jeanbaptiste/textilo/pictures/paper.Textilo/paper-version-of-textilo2.jpg

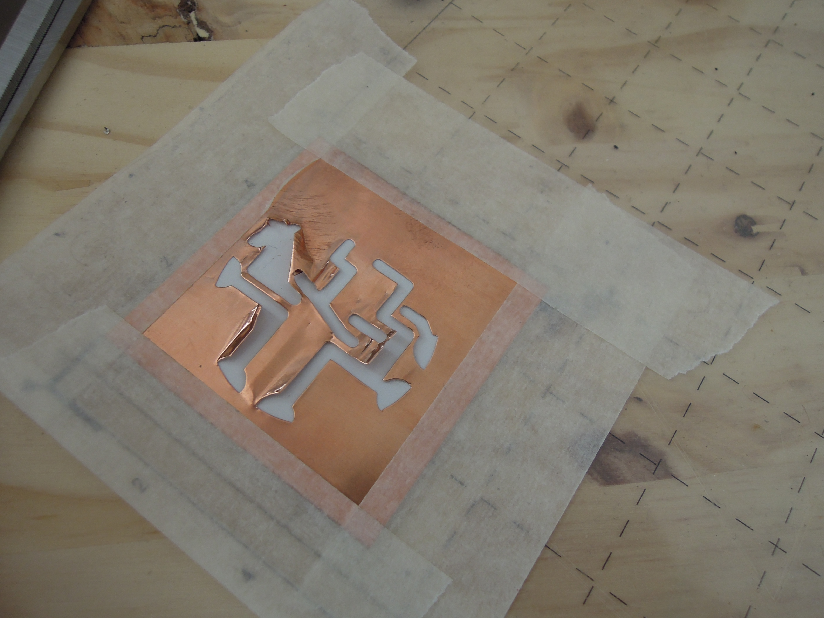
pictures/paper.Textilo/paper-version-of-textilo2.jpg
