jeanbaptiste/textilo/pictures/trial.with.Plotter/555circuit-july.jpg

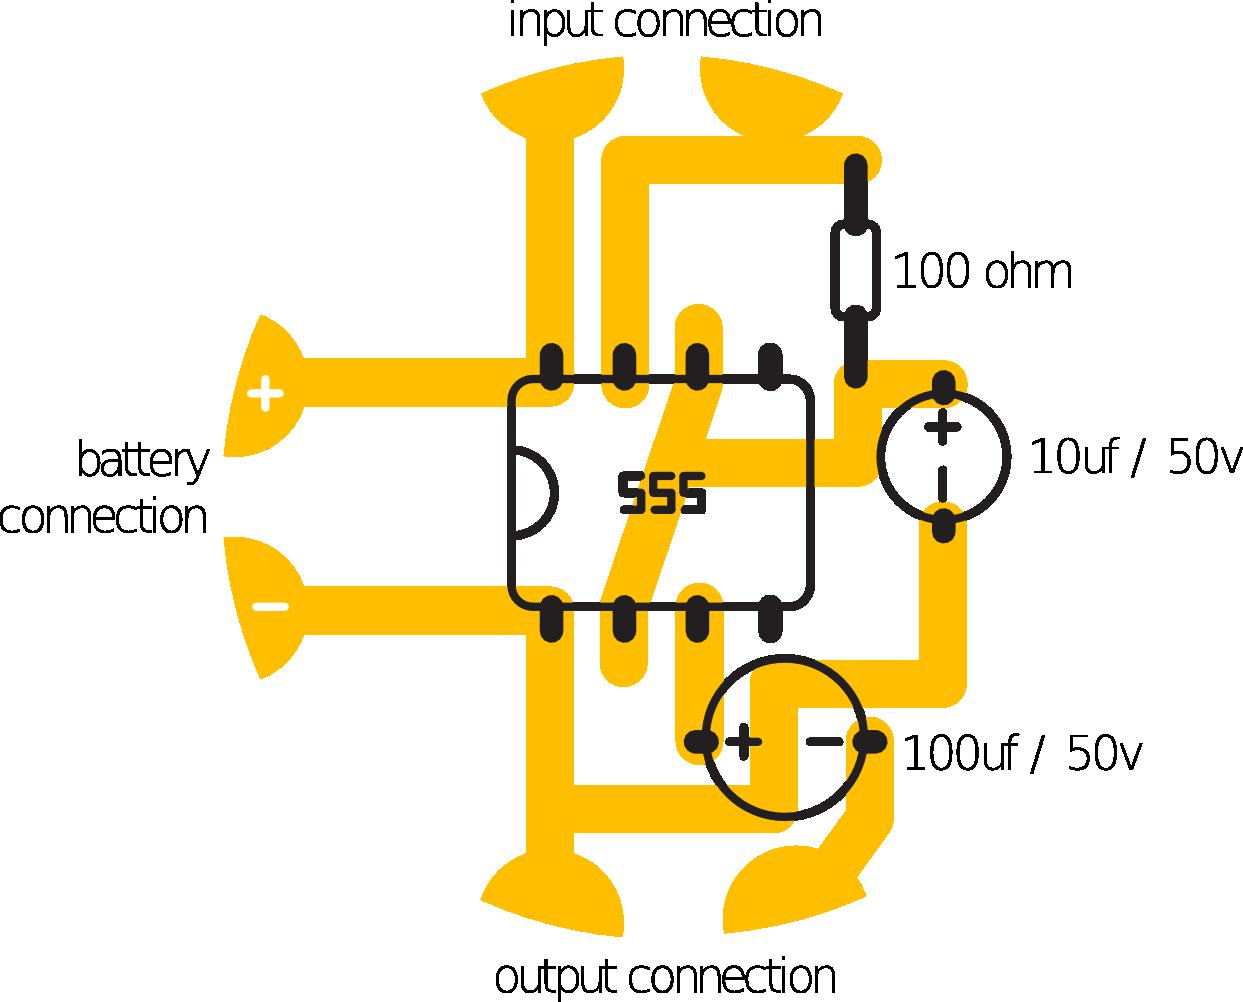
pictures/trial.with.Plotter/555circuit-july.jpg
