jeanbaptiste/textilo/pictures/trial.with.Plotter/EssaiTextilo1.jpg

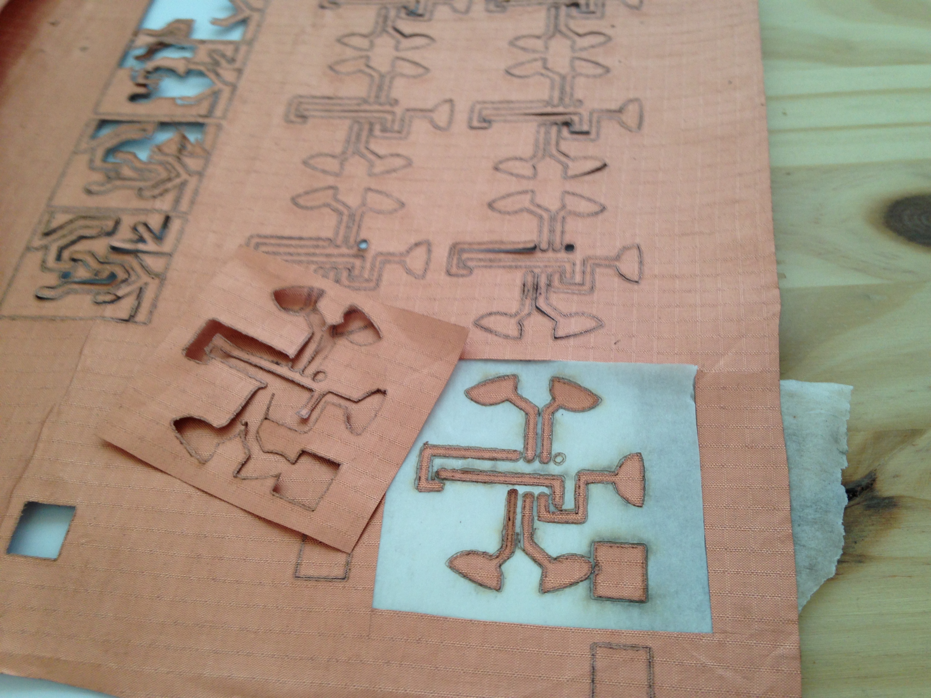
pictures/trial.with.Plotter/EssaiTextilo1.jpg
