jeanbaptiste/textilo/pictures/trial.with.Plotter/EssaiTextilo2.jpg

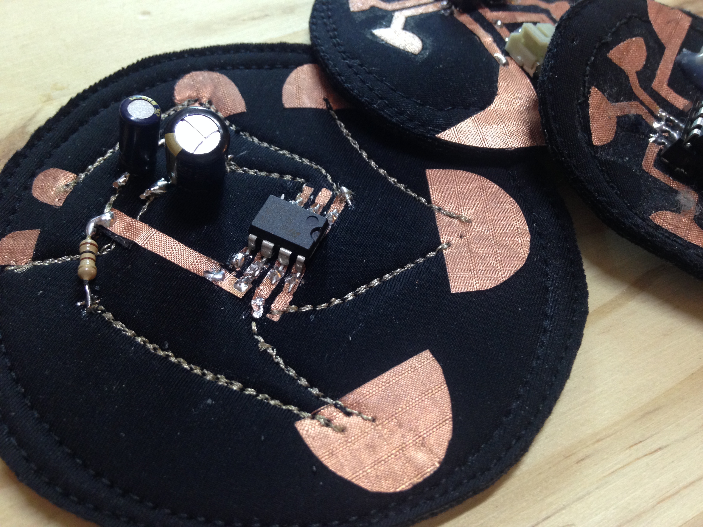
pictures/trial.with.Plotter/EssaiTextilo2.jpg
