jeanbaptiste/textilo/pictures/trial.with.Plotter/EssaiTextilo3.jpg

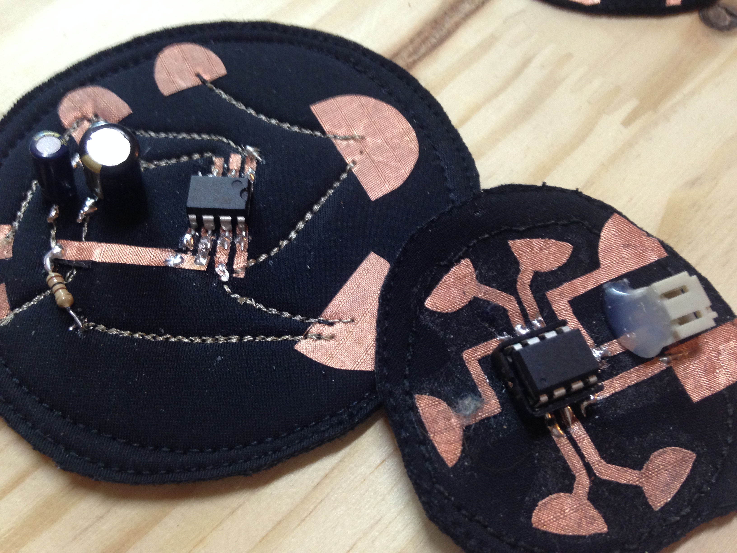
pictures/trial.with.Plotter/EssaiTextilo3.jpg
