jeanbaptiste/textilo/pictures/trial.with.Plotter/EssaiTextilo4.jpg

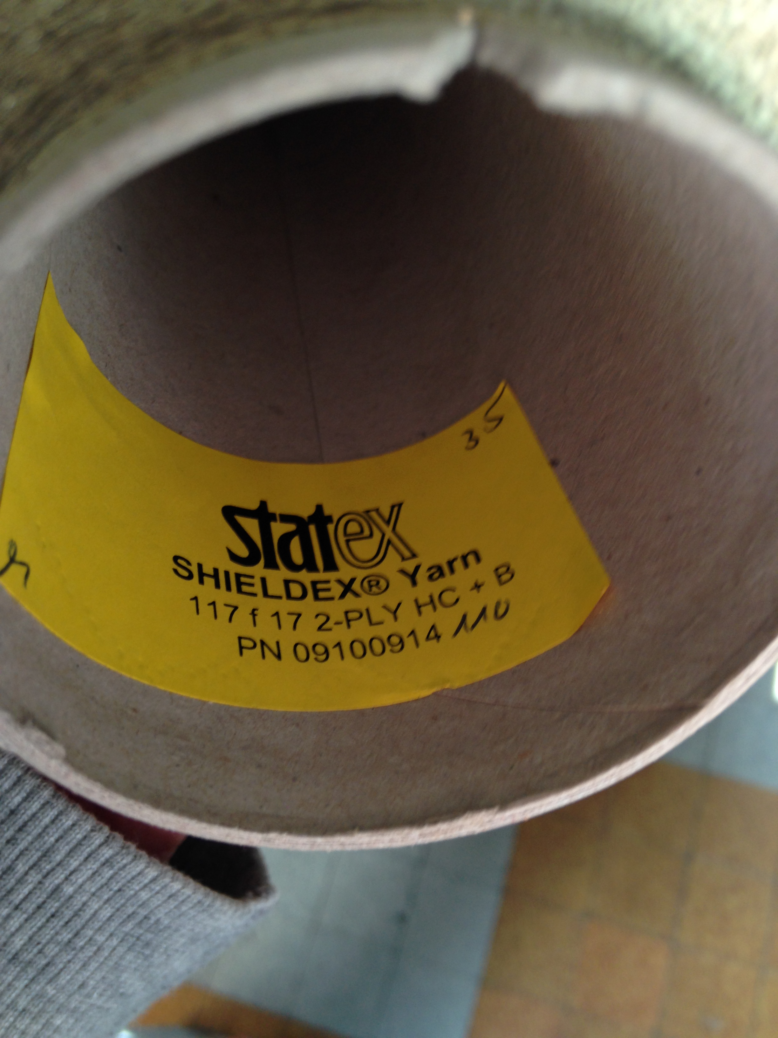
pictures/trial.with.Plotter/EssaiTextilo4.jpg
