jeanbaptiste/textilo/pictures/trial.with.Plotter/EssaiTextilo5.jpg

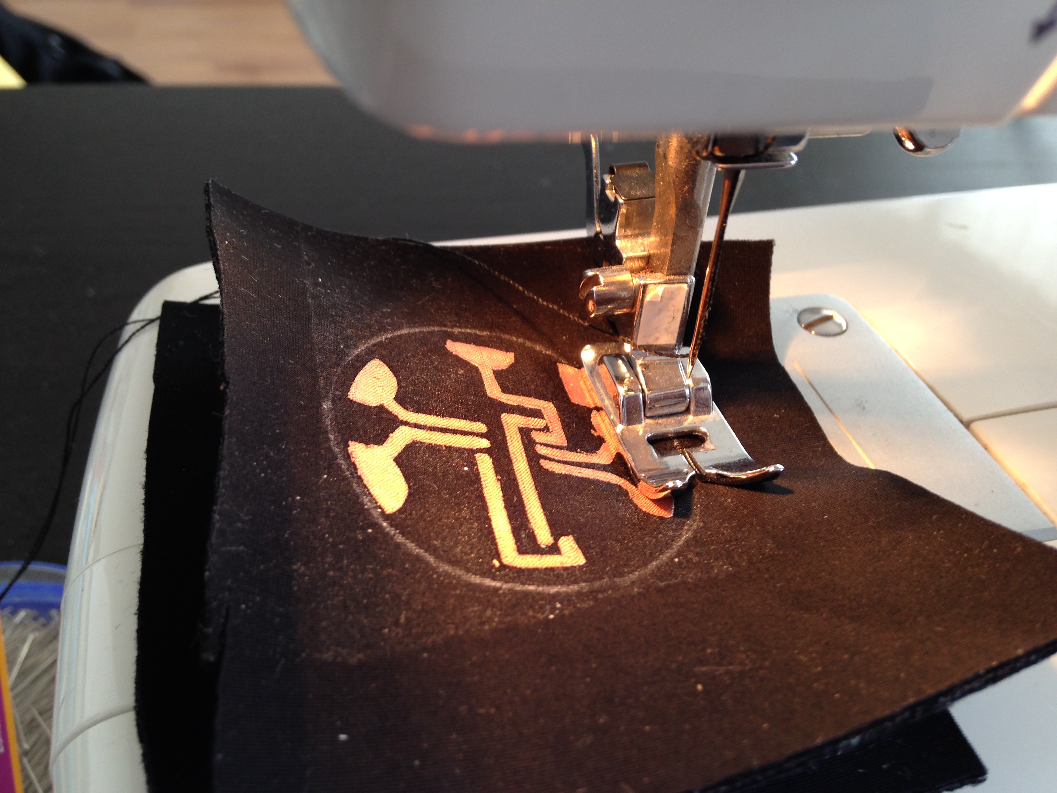
pictures/trial.with.Plotter/EssaiTextilo5.jpg
