jeanbaptiste/textilo/pictures/trial.with.Plotter/EssaiTextilo6.jpg

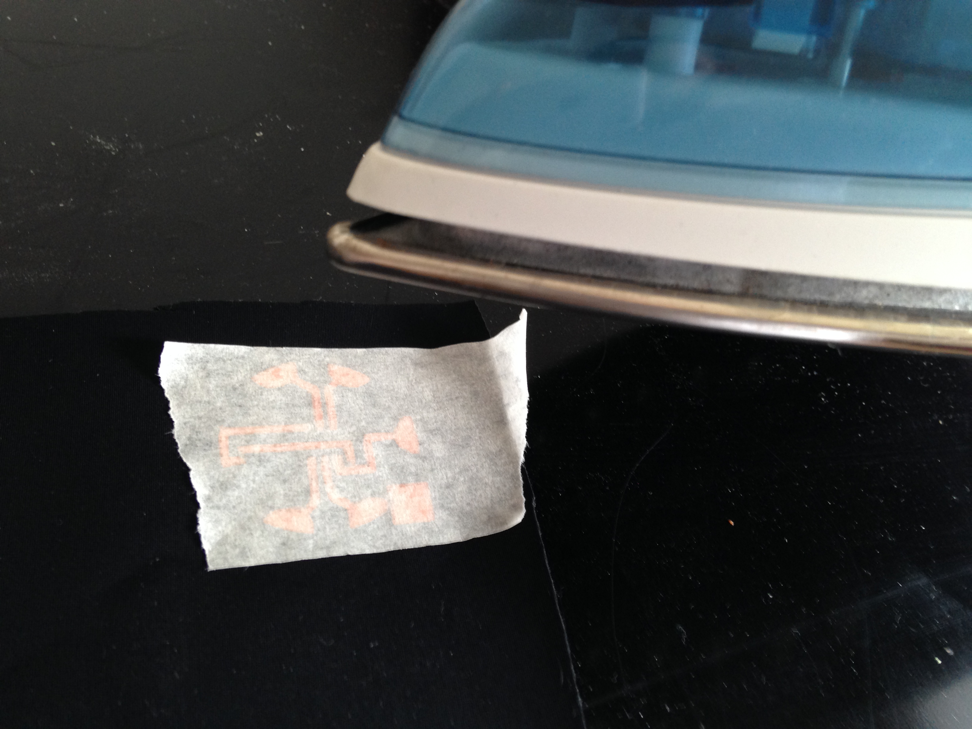
pictures/trial.with.Plotter/EssaiTextilo6.jpg
