jeanbaptiste/textilo/pictures/vinegar.Etch/DSCN3899.JPG

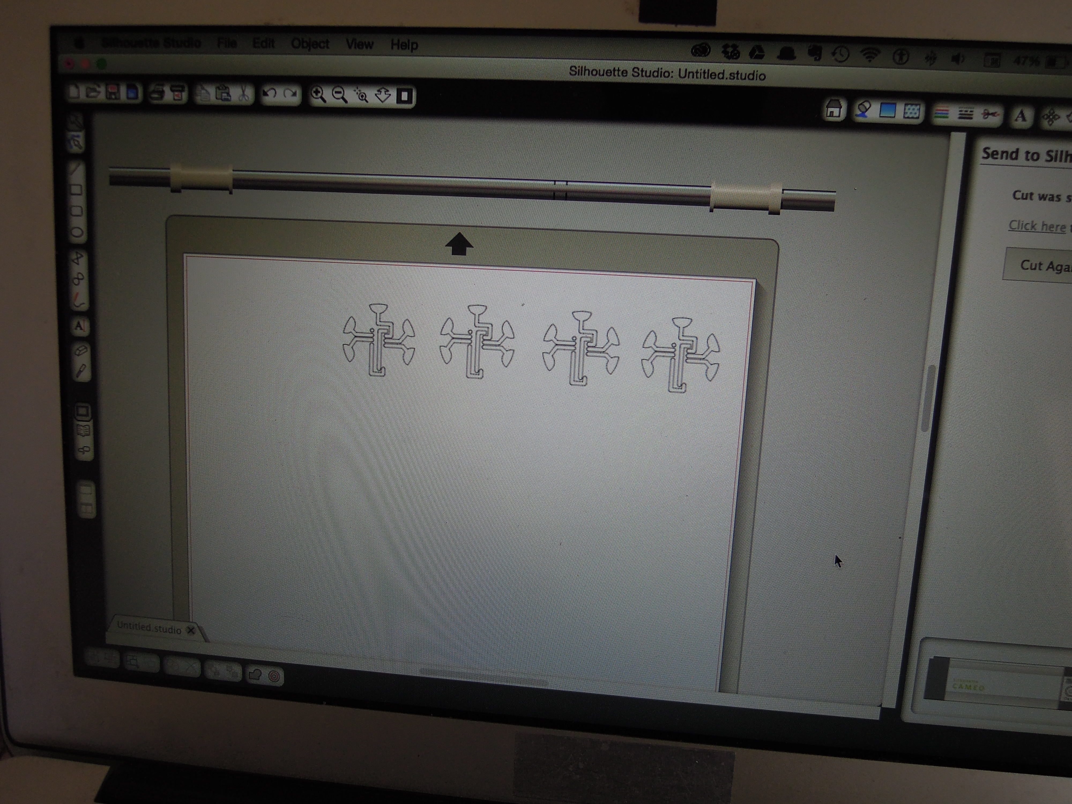
pictures/vinegar.Etch/DSCN3899.JPG
