jeanbaptiste/textilo/pictures/vinegar.Etch/DSCN3900.JPG

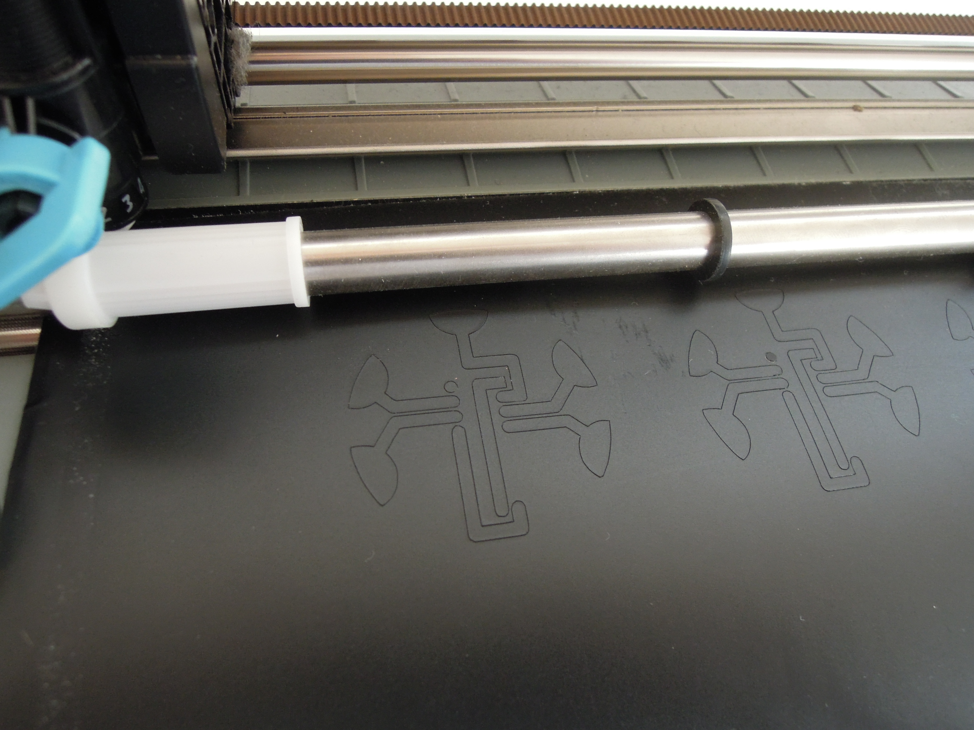
pictures/vinegar.Etch/DSCN3900.JPG
