jeanbaptiste/textilo/pictures/vinegar.Etch/DSCN3902.JPG

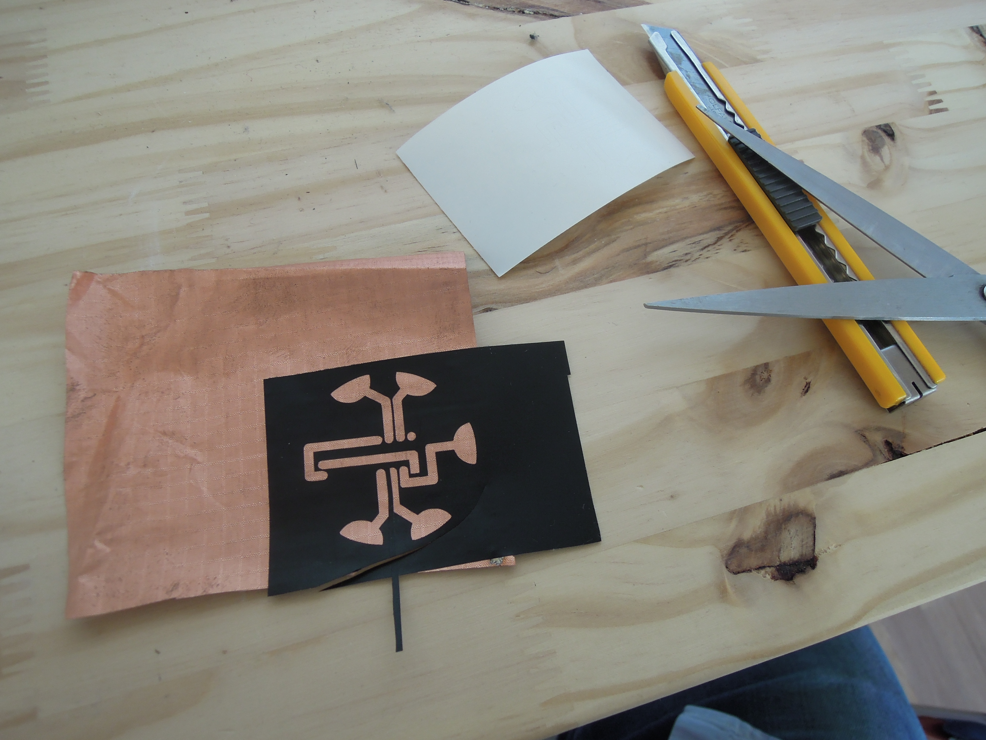
pictures/vinegar.Etch/DSCN3902.JPG
