jeanbaptiste/textilo/pictures/vinegar.Etch/DSCN3903.JPG

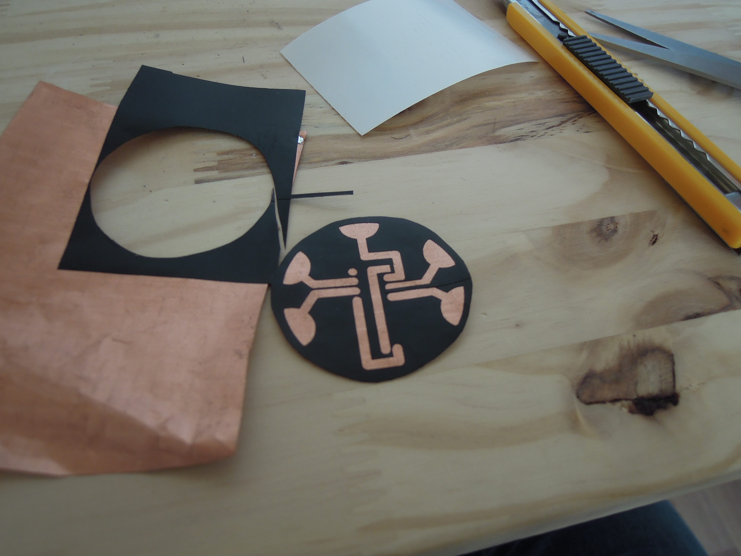
pictures/vinegar.Etch/DSCN3903.JPG
