jeanbaptiste/textilo/pictures/vinegar.Etch/DSCN3904.JPG

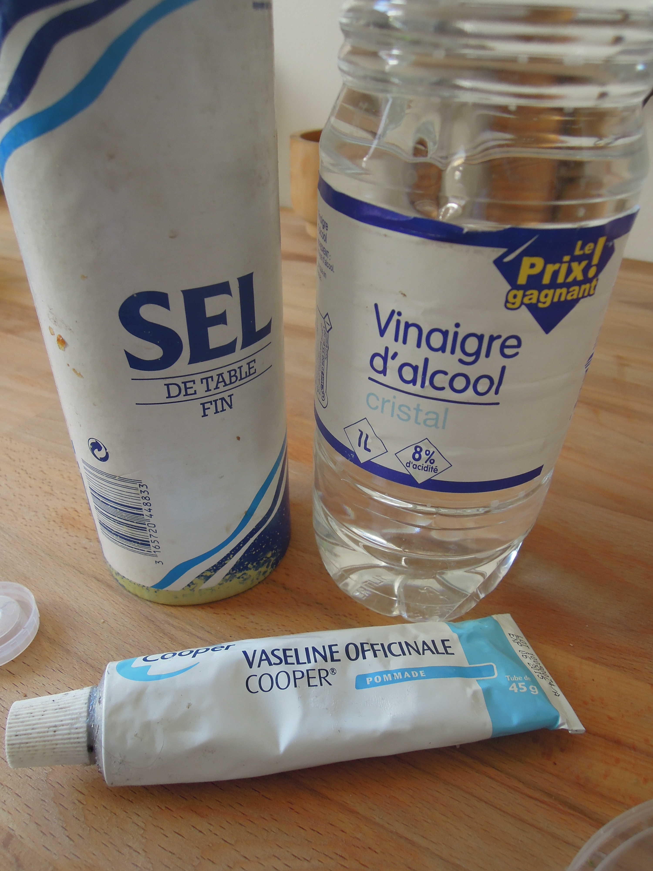
pictures/vinegar.Etch/DSCN3904.JPG
