jeanbaptiste/textilo/pictures/vinegar.Etch/DSCN3905.JPG

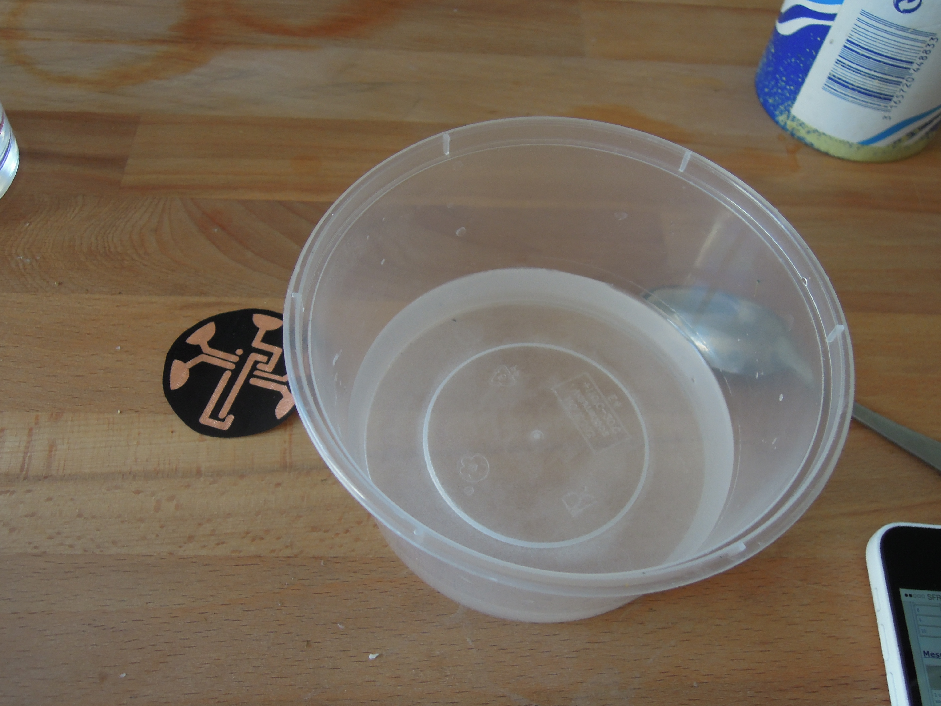
pictures/vinegar.Etch/DSCN3905.JPG
