jeanbaptiste/textilo/pictures/vinegar.Etch/DSCN3906.JPG

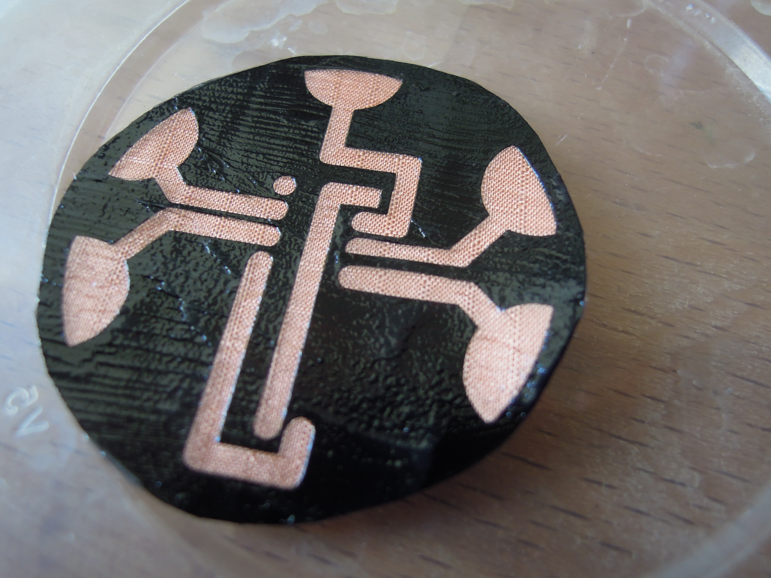
pictures/vinegar.Etch/DSCN3906.JPG
