jeanbaptiste/textilo/pictures/vinegar.Etch/DSCN3907.JPG

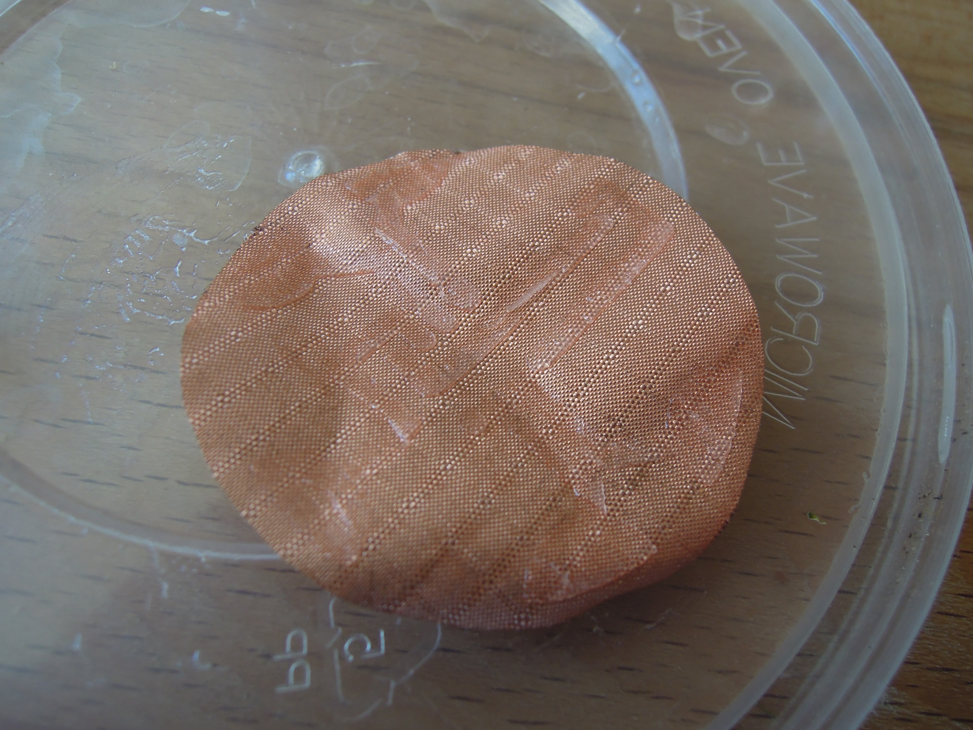
pictures/vinegar.Etch/DSCN3907.JPG
