jeanbaptiste/textilo/pictures/vinegar.Etch/DSCN3908.JPG

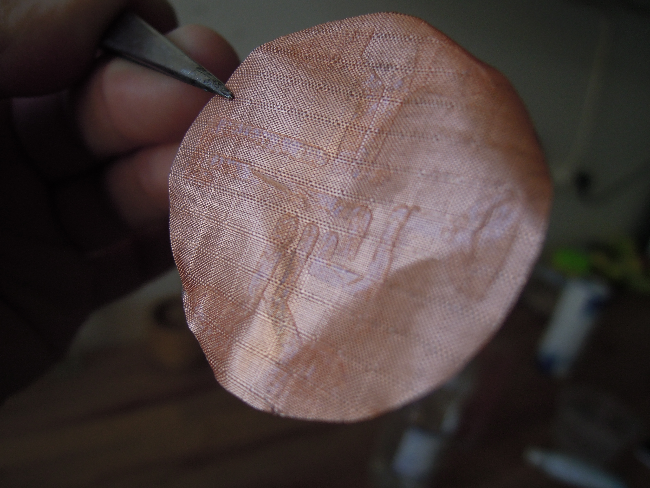
pictures/vinegar.Etch/DSCN3908.JPG
