jeanbaptiste/textilo/pictures/vinegar.Etch/DSCN3909.JPG

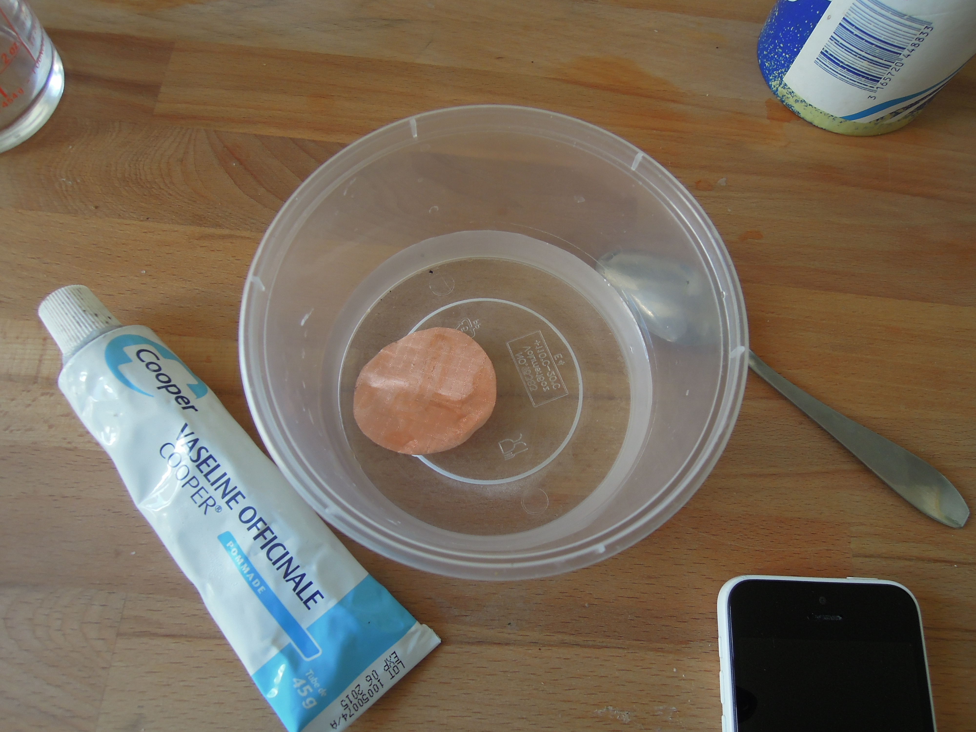
pictures/vinegar.Etch/DSCN3909.JPG
