jeanbaptiste/textilo/pictures/vinegar.Etch/DSCN3911.JPG

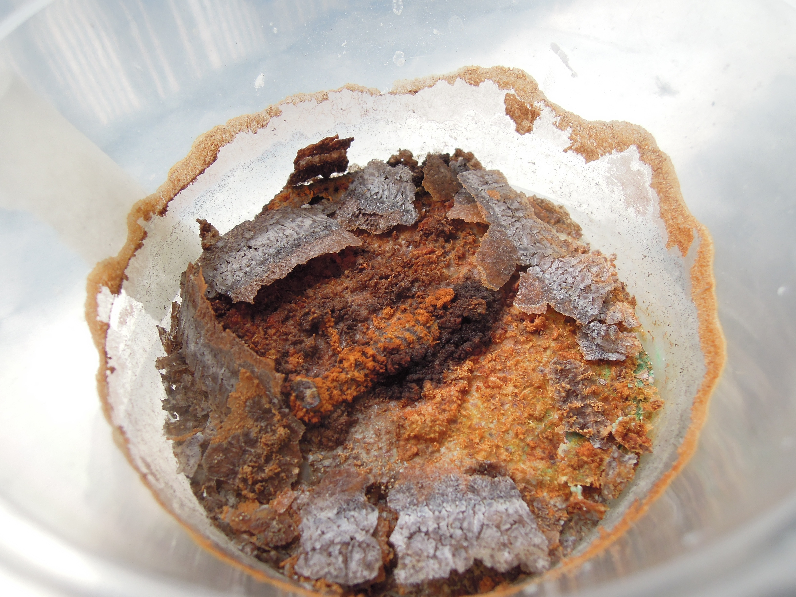
pictures/vinegar.Etch/DSCN3911.JPG
