jeanbaptiste/textilo/pictures/vinegar.Etch/DSCN3912.JPG

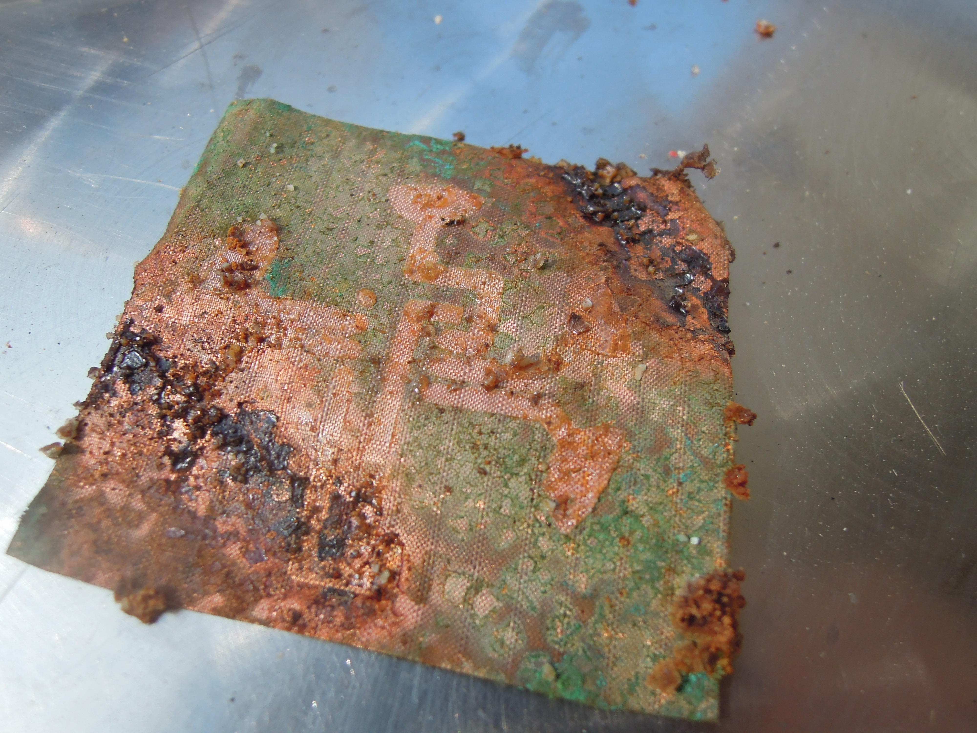
pictures/vinegar.Etch/DSCN3912.JPG
