jeanbaptiste/textilo/pictures/vinegar.Etch/DSCN3913.JPG

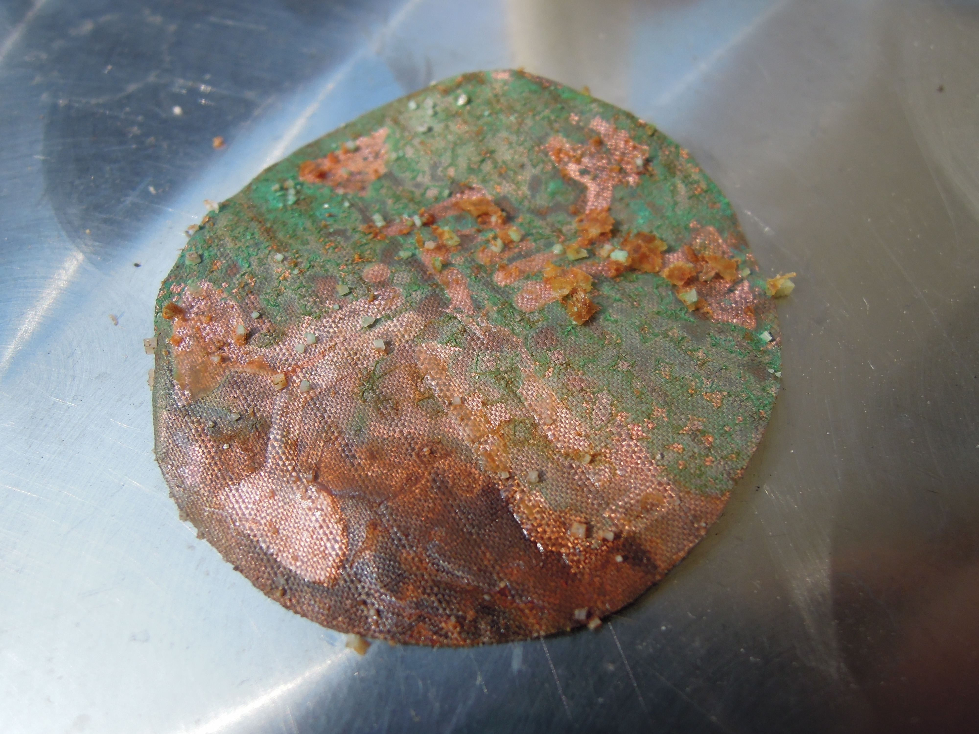
pictures/vinegar.Etch/DSCN3913.JPG
