jeanbaptiste/textilo/pictures/vinegar.Etch/DSCN3914.JPG

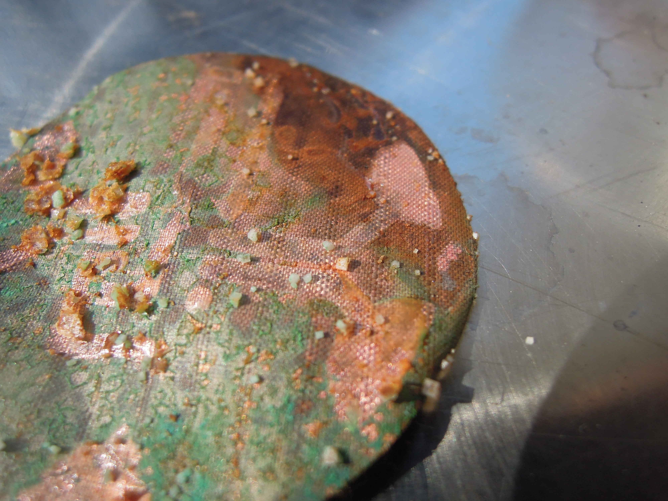
pictures/vinegar.Etch/DSCN3914.JPG
