jeanbaptiste/textilo/pictures/vinegar.Etch/DSCN3915.JPG

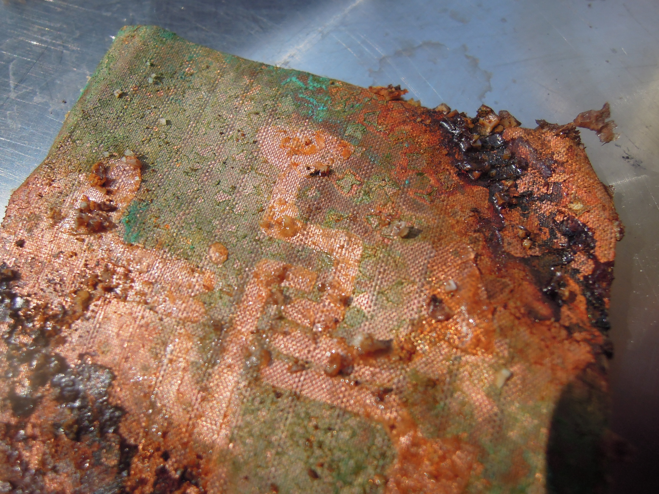
pictures/vinegar.Etch/DSCN3915.JPG
