jeanbaptiste/textilo/pictures/vinegar.Etch/DSCN3916.JPG

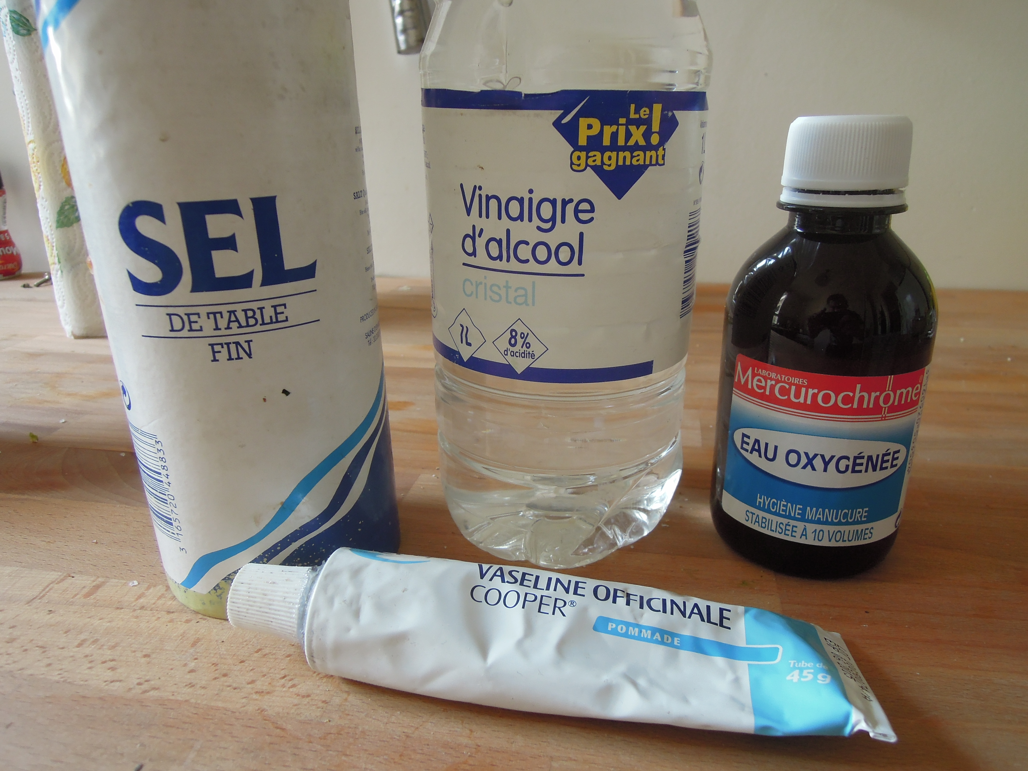
pictures/vinegar.Etch/DSCN3916.JPG
