jeanbaptiste/textilo/pictures/vinegar.Etch/DSCN3917.JPG

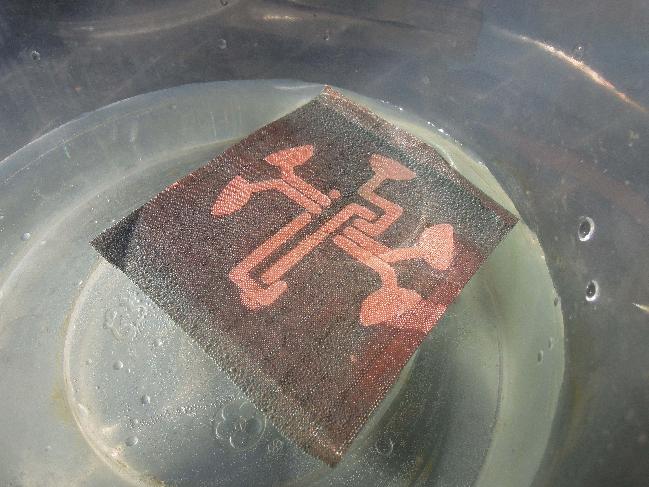
pictures/vinegar.Etch/DSCN3917.JPG
