jeanbaptiste/textilo/pictures/vinegar.Etch/DSCN3918.JPG

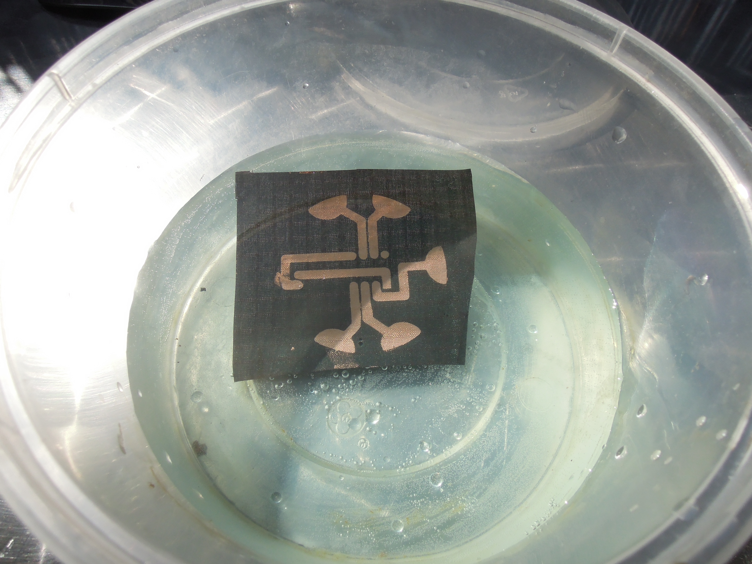
pictures/vinegar.Etch/DSCN3918.JPG
