jeanbaptiste/textilo/pictures/vinegar.Etch/DSCN3919.JPG

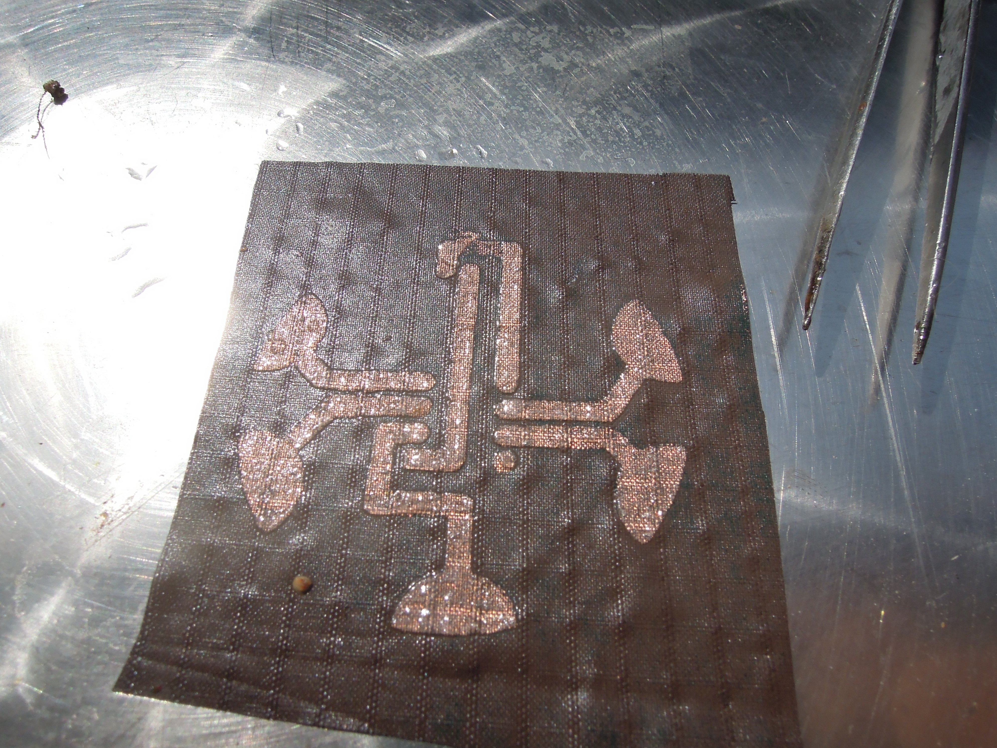
pictures/vinegar.Etch/DSCN3919.JPG
