jeanbaptiste/textilo/pictures/vinegar.Etch/DSCN3920.JPG

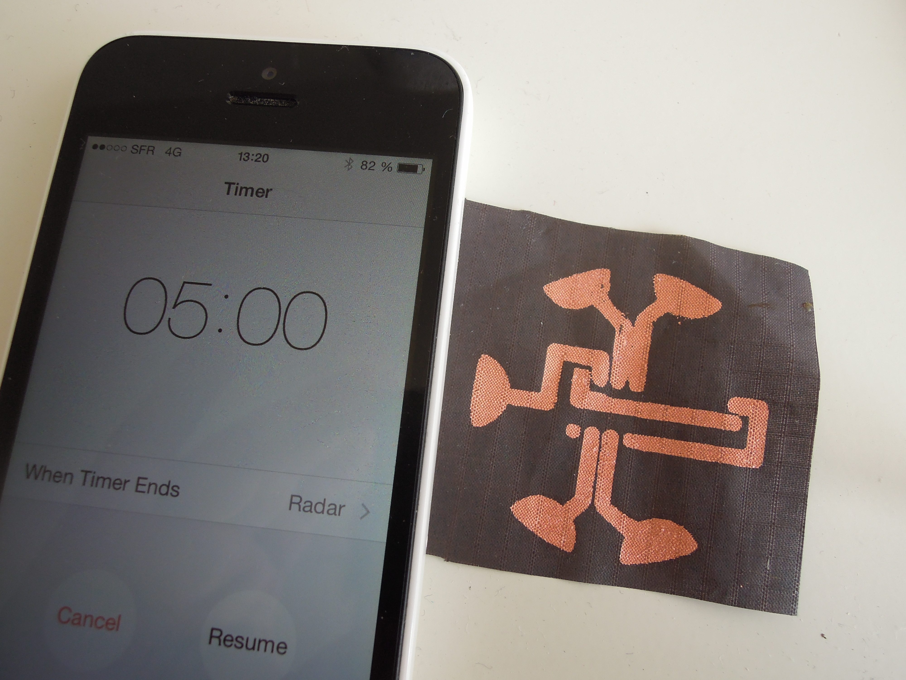
pictures/vinegar.Etch/DSCN3920.JPG
