jeanbaptiste/textilo/pictures/vinegar.Etch/DSCN3921.JPG

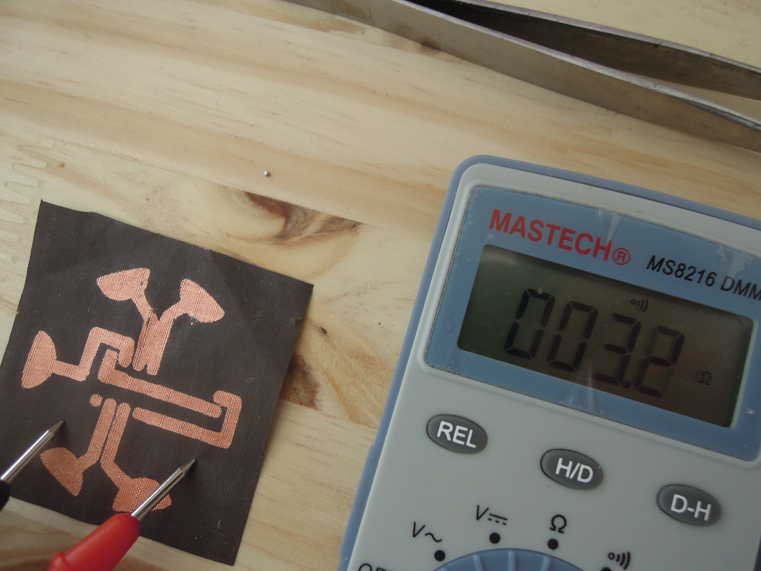
pictures/vinegar.Etch/DSCN3921.JPG
