jeanbaptiste/textilo/pictures/vinegar.Etch/DSCN3923.JPG

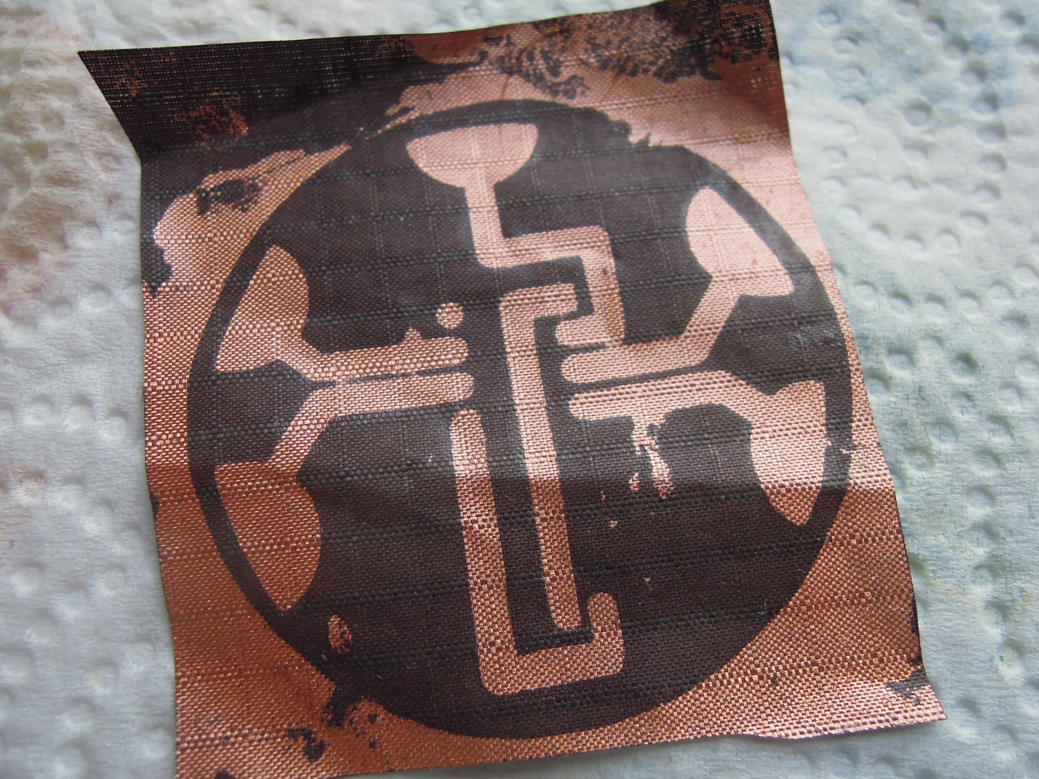
pictures/vinegar.Etch/DSCN3923.JPG
