jeanbaptiste/textilo/pictures/vinegar.Etch/DSCN3924.JPG

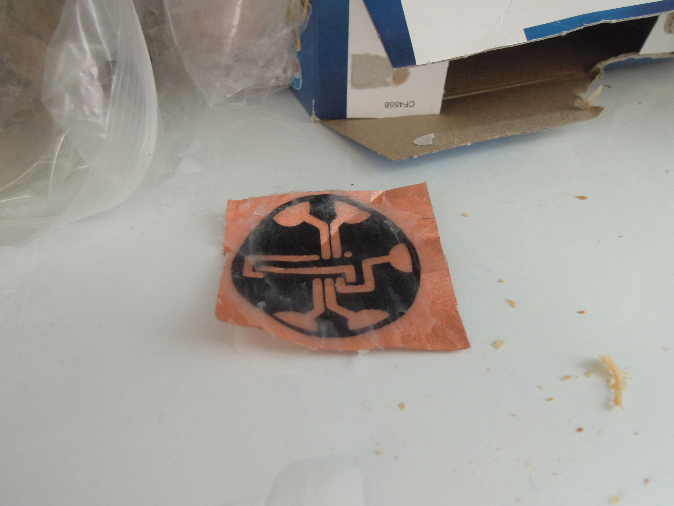
pictures/vinegar.Etch/DSCN3924.JPG
