jeanbaptiste/textilo/pictures/vinegar.Etch/Photo on 12-06-15 at 13.34.jpg

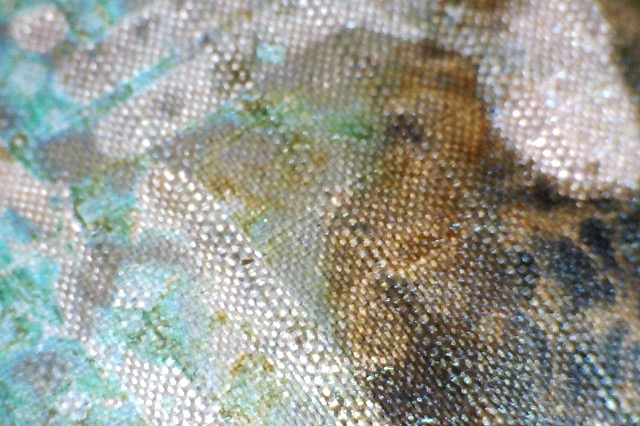
pictures/vinegar.Etch/Photo on 12-06-15 at 13.34.jpg
