jeanbaptiste/textilo/pictures/testrun.Textilo.DataPaulette.July/IMG_0797.JPG

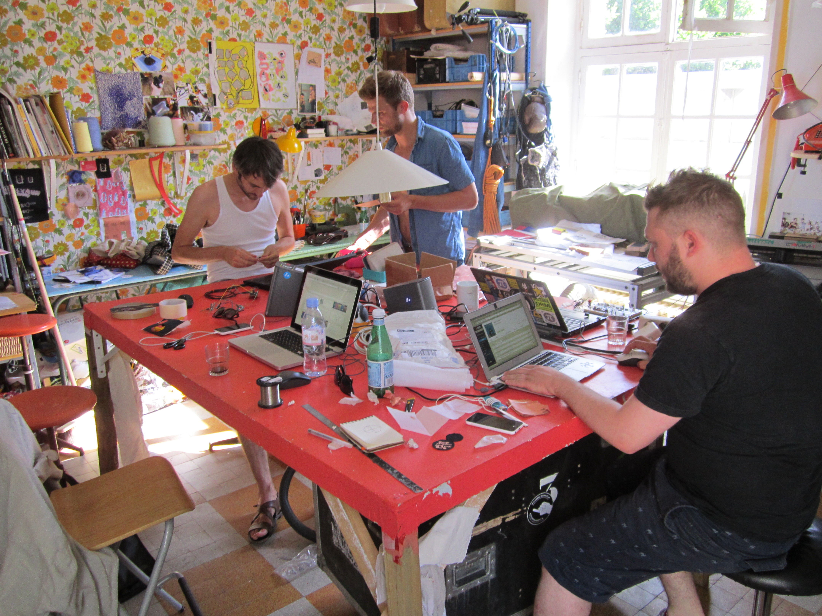
pictures/testrun.Textilo.DataPaulette.July/IMG_0797.JPG
