jeanbaptiste/textilo/pictures/testrun.Textilo.DataPaulette.July/IMG_0798.JPG

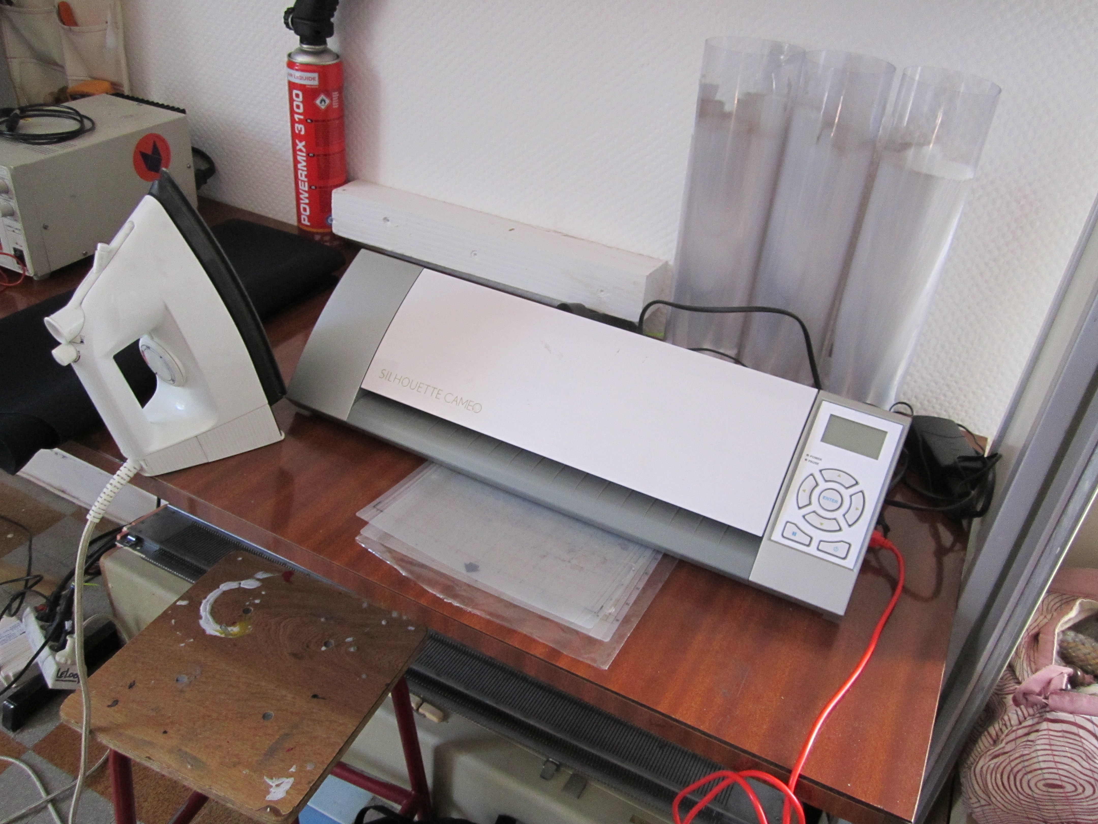
pictures/testrun.Textilo.DataPaulette.July/IMG_0798.JPG
