jeanbaptiste/textilo/pictures/testrun.Textilo.DataPaulette.July/IMG_0800.JPG

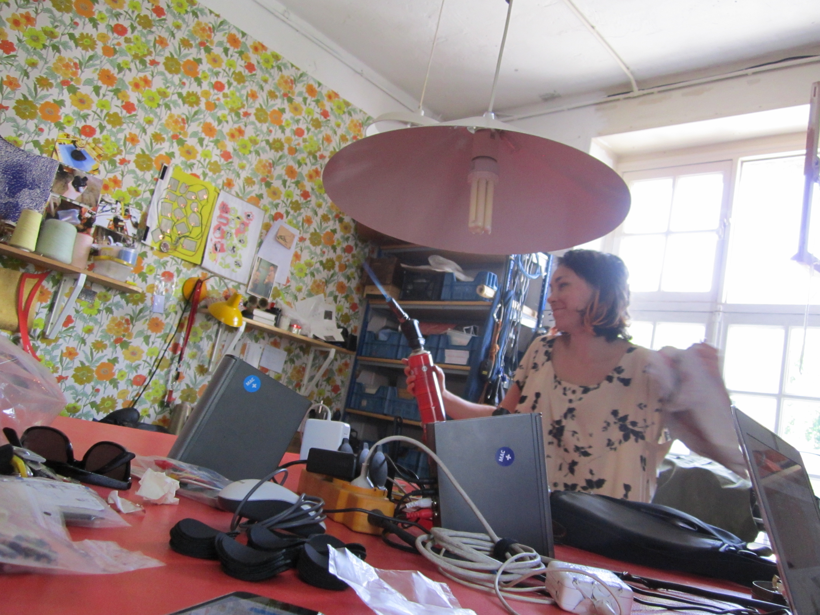
pictures/testrun.Textilo.DataPaulette.July/IMG_0800.JPG
