jeanbaptiste/textilo/pictures/testrun.Textilo.DataPaulette.July/IMG_0802.JPG

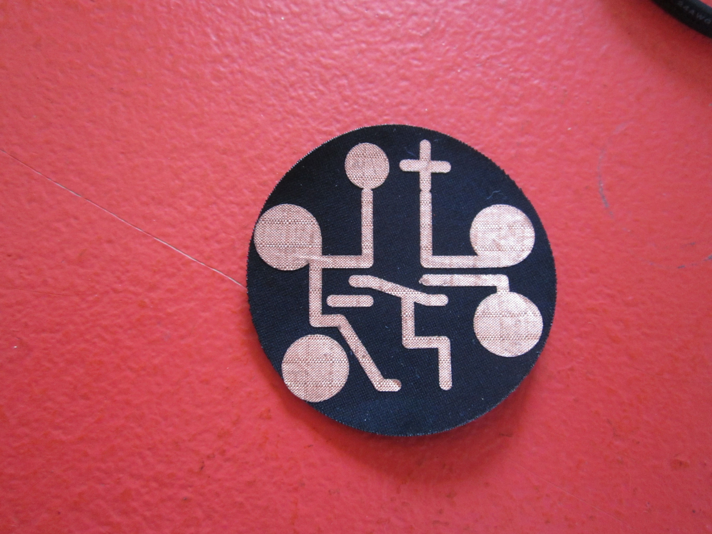
pictures/testrun.Textilo.DataPaulette.July/IMG_0802.JPG
