jeanbaptiste/textilo/pictures/testrun.Textilo.DataPaulette.July/IMG_0803.JPG

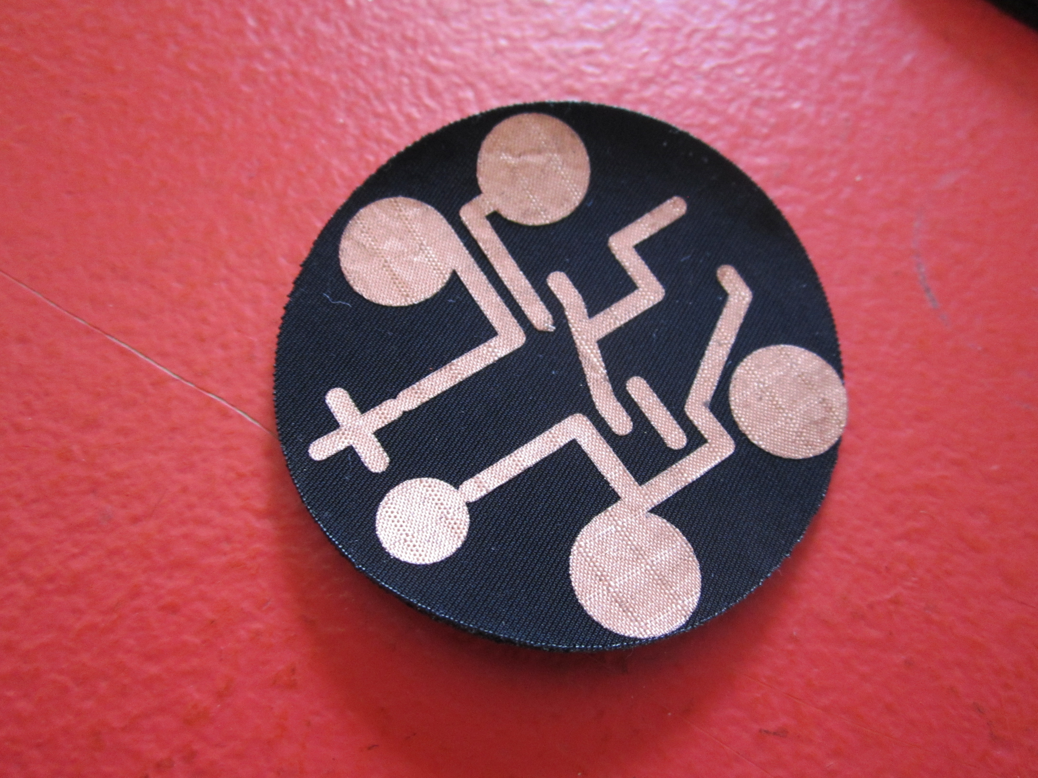
pictures/testrun.Textilo.DataPaulette.July/IMG_0803.JPG
