jeanbaptiste/textilo/pictures/testrun.Textilo.DataPaulette.July/IMG_0804.JPG

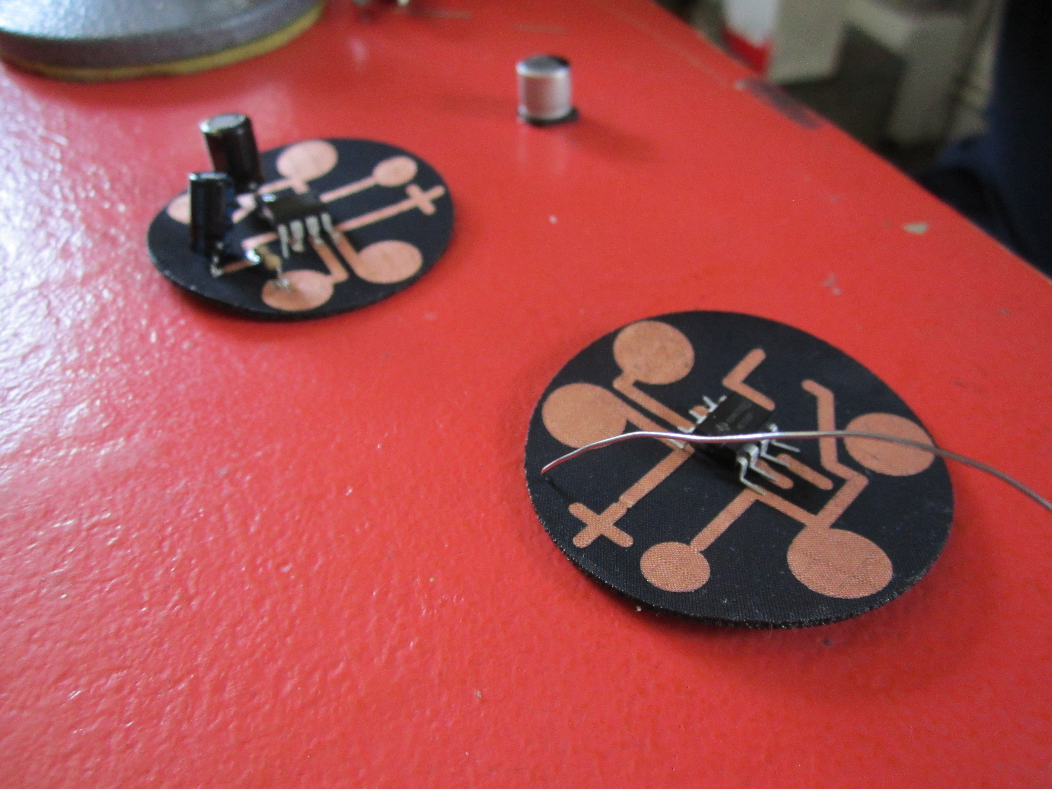
pictures/testrun.Textilo.DataPaulette.July/IMG_0804.JPG
