jeanbaptiste/textilo/pictures/testrun.Textilo.DataPaulette.July/IMG_0805.JPG

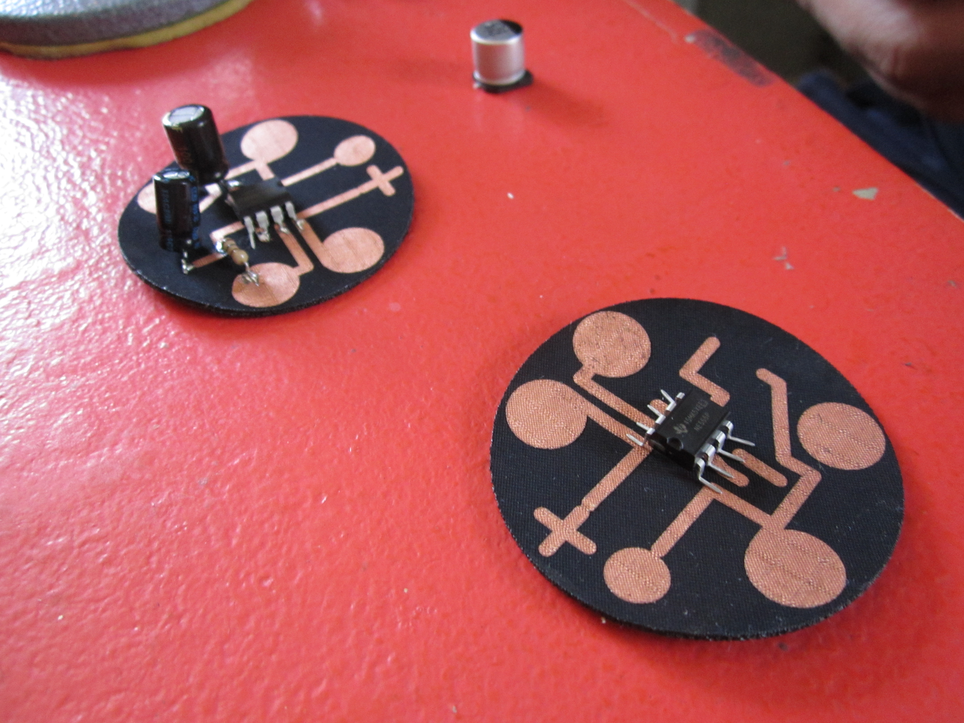
pictures/testrun.Textilo.DataPaulette.July/IMG_0805.JPG
