jeanbaptiste/textilo/pictures/testrun.Textilo.DataPaulette.July/IMG_0806.JPG

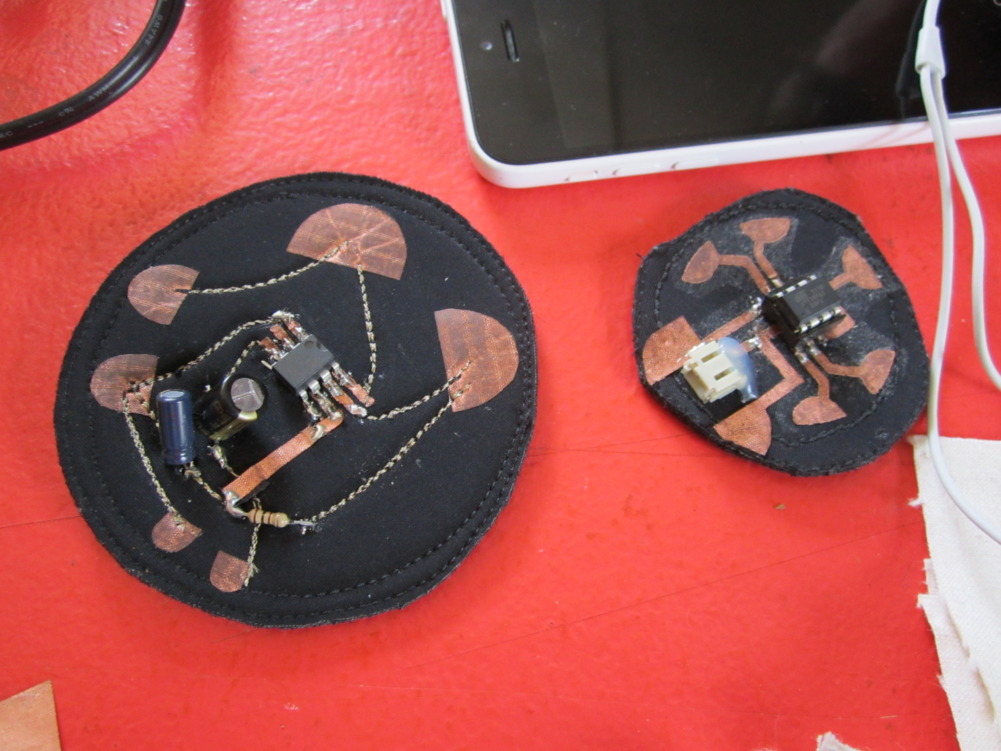
pictures/testrun.Textilo.DataPaulette.July/IMG_0806.JPG
