jeanbaptiste/textilo/pictures/testrun.Textilo.DataPaulette.July/IMG_0807.JPG

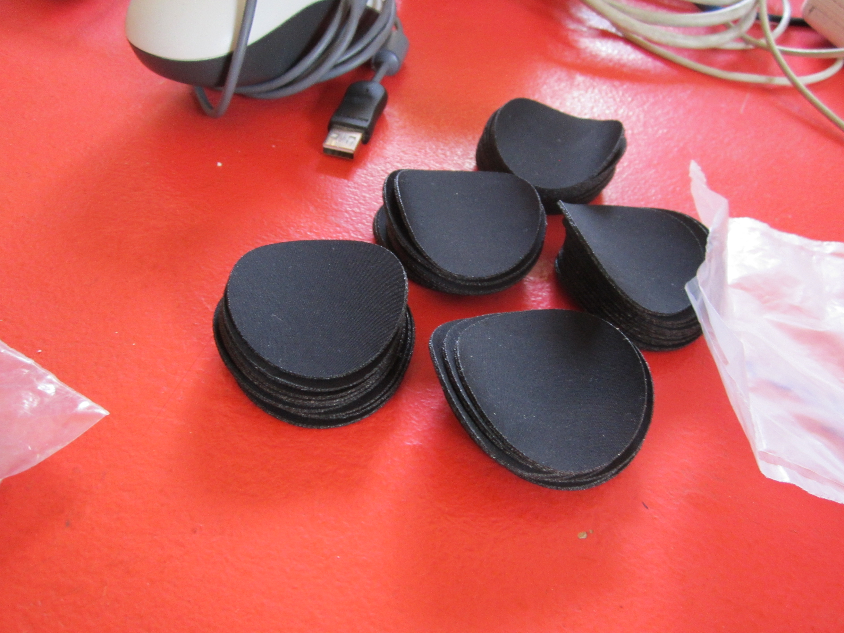
pictures/testrun.Textilo.DataPaulette.July/IMG_0807.JPG
