jeanbaptiste/textilo/pictures/testrun.Textilo.DataPaulette.July/IMG_0808.JPG

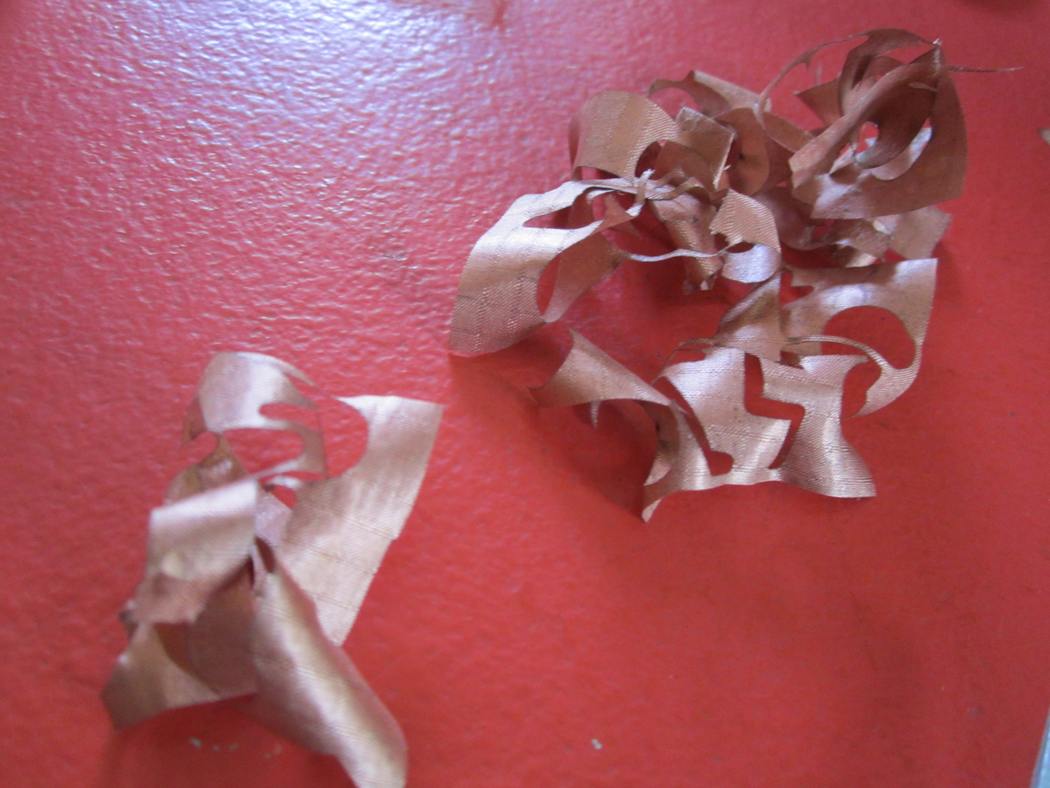
pictures/testrun.Textilo.DataPaulette.July/IMG_0808.JPG
