jeanbaptiste/textilo/pictures/testrun.Textilo.DataPaulette.July/IMG_0811.JPG

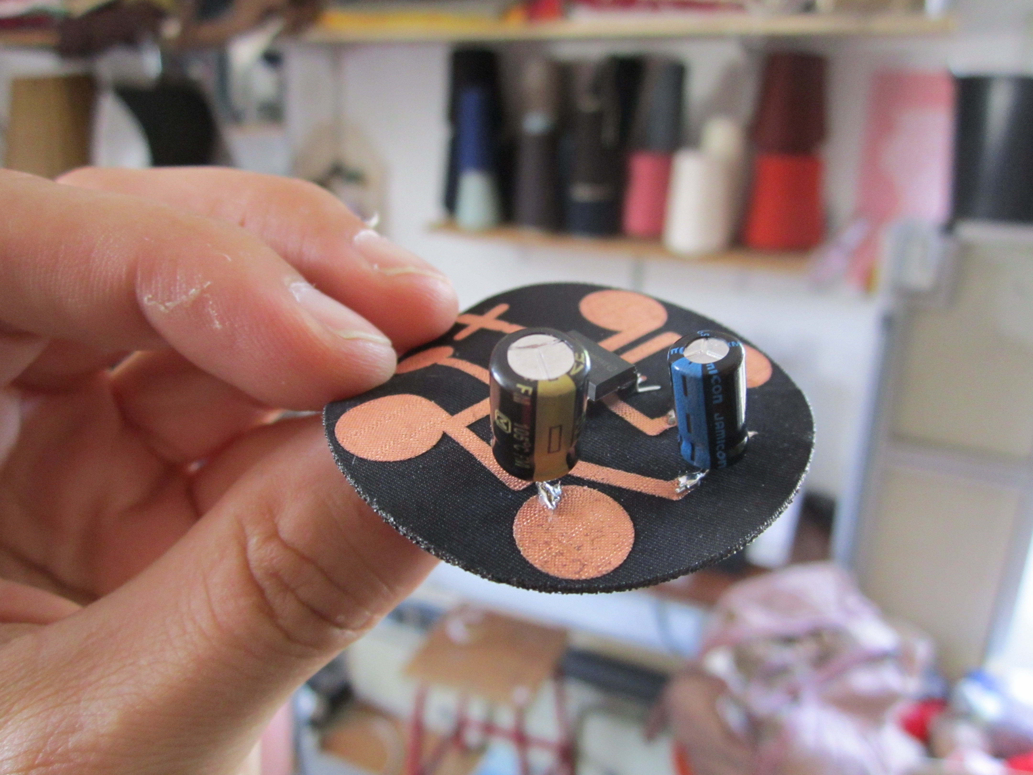
pictures/testrun.Textilo.DataPaulette.July/IMG_0811.JPG
