jeanbaptiste/textilo/pictures/testrun.Textilo.DataPaulette.July/IMG_0812.JPG

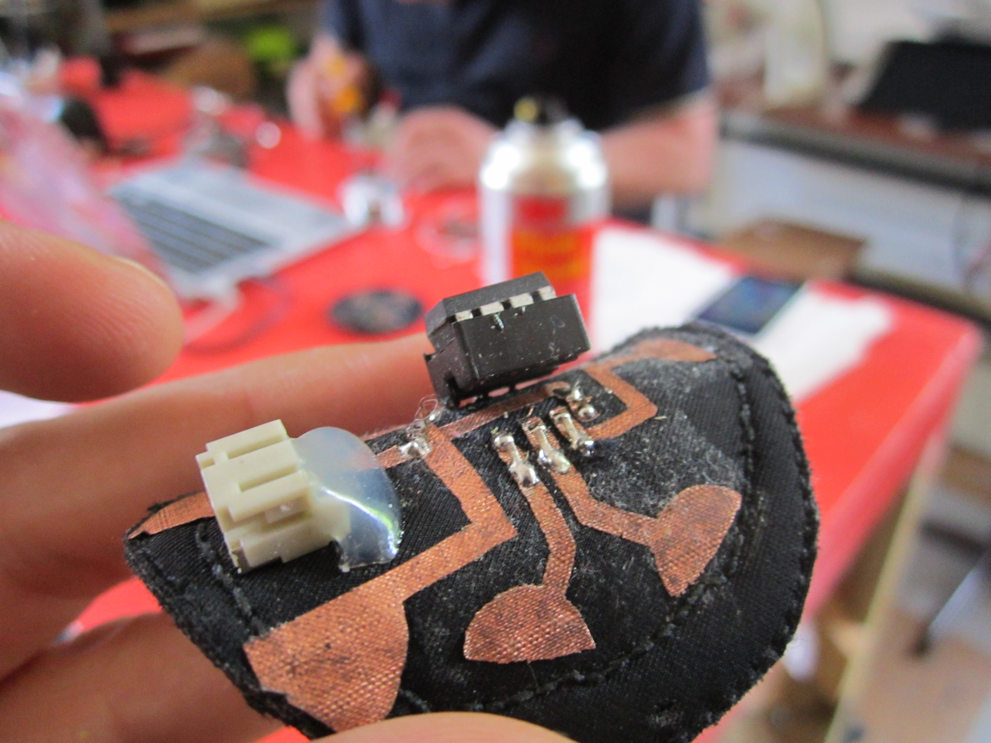
pictures/testrun.Textilo.DataPaulette.July/IMG_0812.JPG
