jeanbaptiste/textilo/pictures/testrun.Textilo.DataPaulette.July/IMG_0853.JPG

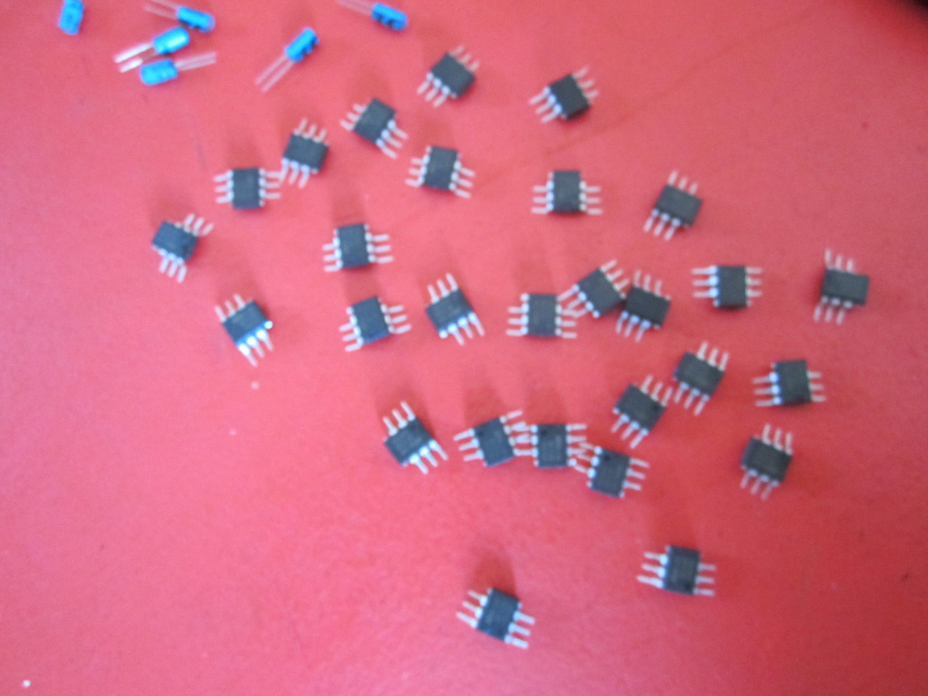
pictures/testrun.Textilo.DataPaulette.July/IMG_0853.JPG
