jeanbaptiste/textilo/pictures/testrun.Textilo.DataPaulette.July/IMG_0858.JPG

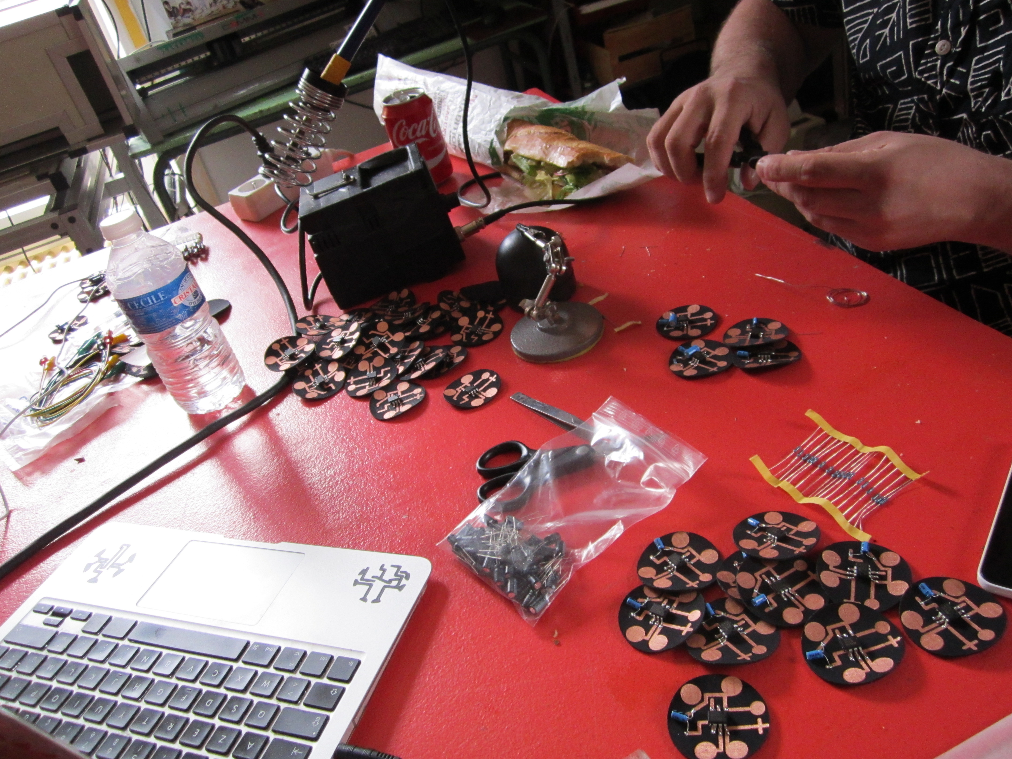
pictures/testrun.Textilo.DataPaulette.July/IMG_0858.JPG
