jeanbaptiste/textilo/pictures/testrun.Textilo.DataPaulette.July/IMG_0801.JPG

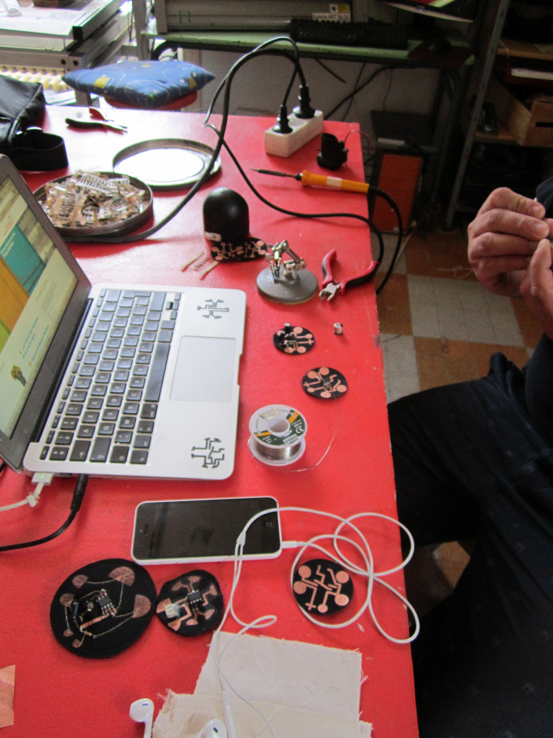
pictures/testrun.Textilo.DataPaulette.July/IMG_0801.JPG
