jeanbaptiste/textilo/pictures/testrun.Textilo.DataPaulette.July/IMG_0809.JPG

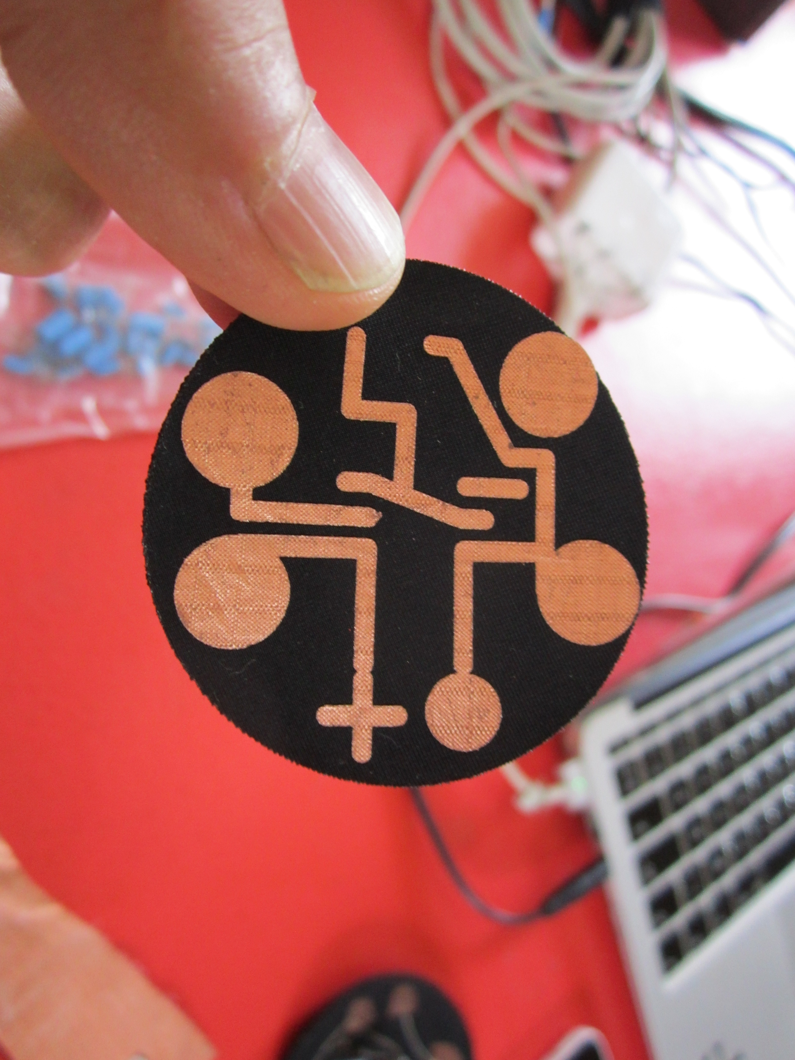
pictures/testrun.Textilo.DataPaulette.July/IMG_0809.JPG
