jeanbaptiste/textilo/pictures/testrun.Textilo.DataPaulette.July/IMG_0810.JPG

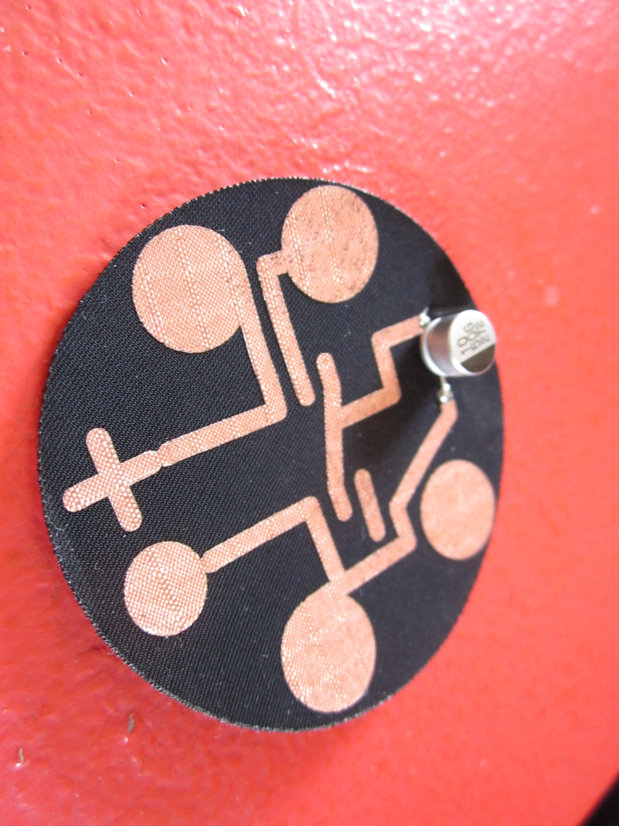
pictures/testrun.Textilo.DataPaulette.July/IMG_0810.JPG
